OpenARDF/Arducon/Software/AtmelStudio7/Arducon/Arducon/EepromManager.cpp

/*
 *  MIT License
 *
 *  Copyright (c) 2021 DigitalConfections
 *
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
 *  THE SOFTWARE IS PROVIDED "AS IS", WITHOUT WARRANTY OF ANY KIND, EXPRESS OR
 *  IMPLIED, INCLUDING BUT NOT LIMITED TO THE WARRANTIES OF MERCHANTABILITY,
 *  FITNESS FOR A PARTICULAR PURPOSE AND NONINFRINGEMENT. IN NO EVENT SHALL THE
 *  AUTHORS OR COPYRIGHT HOLDERS BE LIABLE FOR ANY CLAIM, DAMAGES OR OTHER
 *  LIABILITY, WHETHER IN AN ACTION OF CONTRACT, TORT OR OTHERWISE, ARISING FROM,
 *  OUT OF OR IN CONNECTION WITH THE SOFTWARE OR THE USE OR OTHER DEALINGS IN THE
 *  SOFTWARE.
 */


#include "EepromManager.h"
#include "linkbus.h"
#include "i2c.h"

#if INCLUDE_RV3028_SUPPORT
#include "rv3028.h"
#endif

#if INCLUDE_DS3231_SUPPORT
#include "ds3231.h"
#endif

#ifdef ATMEL_STUDIO_7
#include <avr/pgmspace.h>
#include <avr/wdt.h>
#include <util/delay.h>
#include <stdio.h>
#include <string.h>
#include <math.h>
#endif  /* ATMEL_STUDIO_7 */

const char PRODUCT_NAME_LONG[] PROGMEM = PRODUCT_NAME_LONG_TXT;
const char HELP_TEXT[] PROGMEM = HELP_TEXT_TXT;
const char TEXT_SET_TIME[] PROGMEM = TEXT_SET_TIME_TXT;
const char TEXT_SET_START[] PROGMEM = TEXT_SET_START_TXT;
const char TEXT_SET_FINISH[] PROGMEM = TEXT_SET_FINISH_TXT;
const char TEXT_SET_ID[] PROGMEM = TEXT_SET_ID_TXT;
const char TEXT_ERR_FINISH_BEFORE_START[] PROGMEM = TEXT_ERR_FINISH_BEFORE_START_TXT;
const char TEXT_ERR_FINISH_IN_PAST[] PROGMEM = TEXT_ERR_FINISH_IN_PAST_TXT;
const char TEXT_ERR_START_IN_PAST[] PROGMEM = TEXT_ERR_START_IN_PAST_TXT;
const char TEXT_ERR_INVALID_TIME[] PROGMEM = TEXT_ERR_INVALID_TIME_TXT;
const char TEXT_ERR_TIME_IN_PAST[] PROGMEM = TEXT_ERR_TIME_IN_PAST_TXT;


static const uint8_t DATA_MODULATION_DEFAULTS[SIZE_OF_DATA_MODULATION] PROGMEM =
{
	31, 31, 29, 27, 24, 21, 17, 14,
	10, 8, 5, 3, 2, 1, 1, 0,
	0, 0, 1, 1, 2, 3, 5, 7,
	10, 13, 17, 20, 24, 27, 29, 31
};

/***********************************************************************
 * Global Variables & String Constants
 *
 * Identify each global with a "g_" prefix
 * Whenever possible limit globals' scope to this file using "static"
 * Use "volatile" for globals shared between ISRs and foreground loop
 ************************************************************************/

const struct EE_prom EEMEM EepromManager::ee_vars =
{
	/* .eeprom_initialization_flag = */ 0,
	/* .eeprom_layout_version = */ 0,
	/* .temperature_table = */ { 0 },
	/* .atmega_temp_calibration = */ 0,
	/* .thermal_shutdown_temperature_c = */ 0,
	/* .max_ever_temperature_tenths = */ 0,
	/* .rv3028_offset = */ 0,
	/* .event_start_epoch = */ 0,
	/* .event_finish_epoch = */ 0,
	/* .days_to_run = */ 0,
	/* .stationID_text = */ "\0",

	/* .dataModulation = */ { 0 },
	/* .unlockCode = */ EEPROM_DTMF_UNLOCK_CODE_DEFAULT,

	/* .id_codespeed = */ 0,
	/* .fox_setting = */ 0,
	/* .am_audio_frequency = */ 0,
	/* .utc_offset = */ 0,
	/* .ptt_periodic_reset = */ 0
};

extern char g_messages_text[][MAX_PATTERN_TEXT_LENGTH + 1];
extern volatile uint8_t g_id_codespeed;
extern volatile uint8_t g_pattern_codespeed;
extern volatile uint16_t g_time_needed_for_ID;
extern volatile int16_t g_atmega_temp_calibration;
extern volatile int8_t g_thermal_shutdown_temperature_c;
extern volatile int16_t g_max_ever_temperature_tenths;
extern volatile uint8_t g_temperature_check_countdown;
extern volatile int16_t g_rv3028_offset;

extern volatile Fox_t g_fox;
extern volatile AM_Tone_Freq_t g_AM_audio_frequency;
extern volatile time_t g_event_start_epoch;
extern volatile time_t g_event_finish_epoch;
extern volatile uint8_t g_days_to_run;
extern volatile int8_t g_utc_offset;
extern volatile uint8_t g_ptt_periodic_reset_enabled;

extern uint8_t g_dataModulation[];
extern uint8_t g_unlockCode[];

extern char g_tempStr[];

#define EEPROM_TEXT_TX_IDLE_WAIT_LIMIT 1000

static uint8_t eepromReadByteOrDefault(
	const uint8_t *address,
	uint8_t minimum,
	uint8_t maximum,
	uint8_t defaultValue)
{
	uint8_t value = eeprom_read_byte(address);

	if((value < minimum) || (value > maximum))
	{
		value = defaultValue;
		eeprom_write_byte((uint8_t*)address, value);
	}

	return value;
}

static uint8_t eepromReadBoolOrDefault(
	const uint8_t *address,
	uint8_t defaultValue)
{
	uint8_t value = eeprom_read_byte(address);

	if(value > 1)
	{
		value = defaultValue;
		eeprom_write_byte((uint8_t*)address, value);
	}

	return value;
}

/* default constructor */
EepromManager::EepromManager()
{
}   /*EepromManager */

/* default destructor */
EepromManager::~EepromManager()
{
}   /*~EepromManager */

void EepromManager::updateEEPROMVar(EE_var_t v, void* val)
{
	uint8_t* ee_byte_addr = NULL;
	uint16_t* ee_word_addr = NULL;
	uint32_t* ee_dword_addr = NULL;

	if(!val)
	{
		return;
	}

	switch(v)
	{
		case StationID_text:
		{
			char* char_addr = (char*)val;
			char c = *char_addr++;
			int i = 0;

			while(c && (i < MAX_PATTERN_TEXT_LENGTH))
			{
				eeprom_update_byte((uint8_t*)&(EepromManager::ee_vars.stationID_text[i++]), (uint8_t)c);
				c = *char_addr++;
			}

			eeprom_update_byte((uint8_t*)&(EepromManager::ee_vars.stationID_text[i]), 0);
		}
		break;

		case UnlockCode:
		{
			uint8_t* uint8_addr = (uint8_t*)val;
			uint8_t c = *uint8_addr++;
			int i = 0;

			while(c && (i < MAX_UNLOCK_CODE_LENGTH))
			{
				eeprom_update_byte((uint8_t*)&(EepromManager::ee_vars.unlockCode[i++]), c);
				c = *uint8_addr++;
			}

			eeprom_update_byte((uint8_t*)&(EepromManager::ee_vars.unlockCode[i]), 0);
		}
		break;

		case Id_codespeed:
		{
			ee_byte_addr = (uint8_t*)&(EepromManager::ee_vars.id_codespeed);
		}
		break;

		case Fox_setting:
		{
			ee_byte_addr = (uint8_t*)&(EepromManager::ee_vars.fox_setting);
		}
		break;

		case Am_audio_frequency:
		{
			ee_byte_addr = (uint8_t*)&(EepromManager::ee_vars.am_audio_frequency);
		}
		break;

		case Atmega_temp_calibration:
		{
			ee_word_addr = (uint16_t*)&(EepromManager::ee_vars.atmega_temp_calibration);
		}
		break;

		case Thermal_shutdown_temperature_c:
		{
			ee_byte_addr = (uint8_t*)&(EepromManager::ee_vars.thermal_shutdown_temperature_c);
		}
		break;

		case Max_ever_temperature_tenths:
		{
			ee_word_addr = (uint16_t*)&(EepromManager::ee_vars.max_ever_temperature_tenths);
		}
		break;

		case Rv3028_offset:
		{
			ee_word_addr = (uint16_t*)&(EepromManager::ee_vars.rv3028_offset);
		}
		break;

		case Event_start_epoch:
		{
			ee_dword_addr = (uint32_t*)&(EepromManager::ee_vars.event_start_epoch);
		}
		break;

		case Event_finish_epoch:
		{
			ee_dword_addr = (uint32_t*)&(EepromManager::ee_vars.event_finish_epoch);
		}
		break;

		case Days_to_run:
		{
			ee_byte_addr = (uint8_t*)&(EepromManager::ee_vars.days_to_run);
		}
		break;

		case Utc_offset:
		{
			ee_byte_addr = (uint8_t*)&(EepromManager::ee_vars.utc_offset);
		}
		break;

		case Ptt_periodic_reset:
		{
			ee_byte_addr = (uint8_t*)&(EepromManager::ee_vars.ptt_periodic_reset);
		}
		break;

		case Eeprom_initialization_flag:
		{
			ee_word_addr = (uint16_t*)&(EepromManager::ee_vars.eeprom_initialization_flag);
		}
		break;

		default:
		{

		}
		break;
	}

	if(ee_byte_addr)
	{
		eeprom_update_byte(ee_byte_addr, *(uint8_t*)val);
	}
	else if(ee_word_addr)
	{
		eeprom_update_word(ee_word_addr, *(uint16_t*)val);
	}
	else if(ee_dword_addr)
	{
		eeprom_update_dword(ee_dword_addr, *(uint32_t*)val);
	}
}

void EepromManager::sendEEPROMString(EE_var_t v)
{
	const char* fl_addr = NULL;

	if(!lb_enabled())
	{
		return;
	}

	switch(v)
	{
		case TextVersion:
		{
			fl_addr = PRODUCT_NAME_LONG;
		}
		break;

		case TextHelp:
		{
			fl_addr = HELP_TEXT;
		}
		break;

		case TextSetTime:
		{
			fl_addr = TEXT_SET_TIME;
		}
		break;

		case TextSetStart:
		{
			fl_addr = TEXT_SET_START;
		}
		break;

		case TextSetFinish:
		{
			fl_addr = TEXT_SET_FINISH;
		}
		break;

		case TextSetID:
		{
			fl_addr = TEXT_SET_ID;
		}
		break;

		case TextErrFinishB4Start:
		{
			fl_addr = TEXT_ERR_FINISH_BEFORE_START;

		}
		break;

		case TextErrFinishInPast:
		{
			fl_addr = TEXT_ERR_FINISH_IN_PAST;
		}
		break;

		case TextErrStartInPast:
		{
			fl_addr = TEXT_ERR_START_IN_PAST;
		}
		break;

		case TextErrInvalidTime:
		{
			fl_addr = TEXT_ERR_INVALID_TIME;
		}
		break;

		case TextErrTimeInPast:
		{
			fl_addr = TEXT_ERR_TIME_IN_PAST;
		}
		break;

		default:
		{

		}
		break;
	}

	if(fl_addr)
	{
		char c = pgm_read_byte(fl_addr++);
		uint16_t tries = EEPROM_TEXT_TX_IDLE_WAIT_LIMIT;

		while(c)
		{
			lb_echo_char(c);
			c = pgm_read_byte(fl_addr++);

			while(linkbusTxInProgress() && tries)
			{
				_delay_us(100);
				tries--;
			}

			if(!tries)
			{
				break;
			}

			tries = EEPROM_TEXT_TX_IDLE_WAIT_LIMIT;
		}
	}
}

BOOL EepromManager::readNonVols(void)
{
	BOOL failure = TRUE;
	uint16_t i;

	if(eepromLayoutIsCurrent())  /* EEPROM is initialized and matches this firmware layout */
	{
		g_id_codespeed = eepromReadByteOrDefault(
			&(EepromManager::ee_vars.id_codespeed),
			MIN_CODE_SPEED_WPM,
			MAX_CODE_SPEED_WPM,
			EEPROM_ID_CODE_SPEED_DEFAULT);
		g_fox = CLAMP(BEACON, (Fox_t)eeprom_read_byte(&(EepromManager::ee_vars.fox_setting)), SPRINT_F5);
		g_AM_audio_frequency = (AM_Tone_Freq_t)eepromReadByteOrDefault(
			&(EepromManager::ee_vars.am_audio_frequency),
			MIN_AM_TONE_FREQUENCY,
			MAX_AM_TONE_FREQUENCY,
			EEPROM_AM_AUDIO_FREQ_DEFAULT);
		g_atmega_temp_calibration = (int16_t)eeprom_read_word((uint16_t*)&(EepromManager::ee_vars.atmega_temp_calibration));
		g_thermal_shutdown_temperature_c = CLAMP(THERMAL_SHUTDOWN_MIN_C, (int8_t)eeprom_read_byte((uint8_t*)&(EepromManager::ee_vars.thermal_shutdown_temperature_c)), THERMAL_SHUTDOWN_MAX_C);
		g_max_ever_temperature_tenths = (int16_t)eeprom_read_word((uint16_t*)&(EepromManager::ee_vars.max_ever_temperature_tenths));
		g_rv3028_offset = (int16_t)eeprom_read_word((uint16_t*)&(EepromManager::ee_vars.rv3028_offset));
		g_event_start_epoch = eeprom_read_dword(&(EepromManager::ee_vars.event_start_epoch));
		g_event_finish_epoch = eeprom_read_dword(&(EepromManager::ee_vars.event_finish_epoch));
		g_days_to_run = eepromReadByteOrDefault(
			&(EepromManager::ee_vars.days_to_run),
			MIN_DAYS_TO_RUN,
			MAX_DAYS_TO_RUN,
			EEPROM_DAYS_TO_RUN_DEFAULT);
#if INCLUDE_RV3028_SUPPORT
		g_utc_offset = (int8_t)eeprom_read_byte(&(EepromManager::ee_vars.utc_offset));
		if((g_utc_offset < -24) || (g_utc_offset > 24))
		{
			g_utc_offset = EEPROM_UTC_OFFSET_DEFAULT;
			eeprom_write_byte((uint8_t*)&(EepromManager::ee_vars.utc_offset), (uint8_t)g_utc_offset);
		}
#else
		g_utc_offset = EEPROM_UTC_OFFSET_DEFAULT;
		if(eeprom_read_byte(&(EepromManager::ee_vars.utc_offset)) != (uint8_t)EEPROM_UTC_OFFSET_DEFAULT)
		{
			eeprom_write_byte((uint8_t*)&(EepromManager::ee_vars.utc_offset), (uint8_t)EEPROM_UTC_OFFSET_DEFAULT);
		}
#endif
		g_ptt_periodic_reset_enabled = eepromReadBoolOrDefault(
			&(EepromManager::ee_vars.ptt_periodic_reset),
			EEPROM_PTT_PERIODIC_RESET_DEFAULT);

		for(i = 0; i < MAX_PATTERN_TEXT_LENGTH; i++)
		{
			g_messages_text[STATION_ID][i] = (char)eeprom_read_byte((uint8_t*)(&(EepromManager::ee_vars.stationID_text[i])));
			if(!g_messages_text[STATION_ID][i])
			{
				break;
			}
		}
		g_messages_text[STATION_ID][MAX_PATTERN_TEXT_LENGTH] = '\0';

		for(i = 0; i < MAX_UNLOCK_CODE_LENGTH; i++)
		{
			g_unlockCode[i] = (char)eeprom_read_byte((uint8_t*)(&(EepromManager::ee_vars.unlockCode[i])));
			if(!g_unlockCode[i])
			{
				break;
			}
		}
		g_unlockCode[MAX_UNLOCK_CODE_LENGTH] = '\0';

		for(i = 0; i < SIZE_OF_DATA_MODULATION; i++)    /* Use 1-degree steps and take advantage of parabola symmetry for -35C to +85C coverage */
		{
			g_dataModulation[i] = (uint8_t)eeprom_read_byte((uint8_t*)&(EepromManager::ee_vars.dataModulation[i]));
		}

		/* Perform sanity checks */
		if(g_event_start_epoch && (g_event_finish_epoch <= g_event_start_epoch))
		{
			g_event_finish_epoch = g_event_start_epoch + SECONDS_24H;
		}

		failure = FALSE;
	}

	return( failure);
}

BOOL EepromManager::eepromLayoutIsCurrent(void)
{
	uint16_t initialization_flag = eeprom_read_word(&(EepromManager::ee_vars.eeprom_initialization_flag));
	uint16_t layout_version = eeprom_read_word(&(EepromManager::ee_vars.eeprom_layout_version));

	return((initialization_flag == EEPROM_INITIALIZED_FLAG) && (layout_version == EEPROM_LAYOUT_VERSION));
}


/*
 * Initialize EEPROM defaults and mirror mutable defaults into RAM.
 */
BOOL EepromManager::initializeEEPROMVars(void)
{
	uint16_t i;

	g_id_codespeed = EEPROM_ID_CODE_SPEED_DEFAULT;
	eeprom_write_byte((uint8_t*)&(EepromManager::ee_vars.id_codespeed), g_id_codespeed);

		g_fox = EEPROM_FOX_SETTING_DEFAULT;
		eeprom_write_byte((uint8_t*)&(EepromManager::ee_vars.fox_setting), g_fox);

		g_AM_audio_frequency = EEPROM_AM_AUDIO_FREQ_DEFAULT;
		eeprom_write_byte((uint8_t*)&(EepromManager::ee_vars.am_audio_frequency), (uint8_t)g_AM_audio_frequency);

		g_atmega_temp_calibration = EEPROM_TEMP_CALIBRATION_DEFAULT;
		eeprom_write_word((uint16_t*)&(EepromManager::ee_vars.atmega_temp_calibration), (uint16_t)g_atmega_temp_calibration);

		g_thermal_shutdown_temperature_c = EEPROM_THERMAL_SHUTDOWN_TEMP_C_DEFAULT;
		eeprom_write_byte((uint8_t*)&(EepromManager::ee_vars.thermal_shutdown_temperature_c), (uint8_t)g_thermal_shutdown_temperature_c);

		g_max_ever_temperature_tenths = EEPROM_MAX_EVER_TEMPERATURE_TENTHS_DEFAULT;
		eeprom_write_word((uint16_t*)&(EepromManager::ee_vars.max_ever_temperature_tenths), (uint16_t)g_max_ever_temperature_tenths);

		i2c_init(); /* Needs to happen before reading RTC */

#if INCLUDE_RV3028_SUPPORT
		g_rv3028_offset = rv3028_get_offset_RAM();
		eeprom_write_word((uint16_t*)&(EepromManager::ee_vars.rv3028_offset), (uint16_t)g_rv3028_offset);
#endif // INCLUDE_RV3028_SUPPORT

		g_event_start_epoch = EEPROM_START_EPOCH_DEFAULT;
		eeprom_write_dword((uint32_t*)&(EepromManager::ee_vars.event_start_epoch), g_event_start_epoch);

		g_event_finish_epoch = EEPROM_FINISH_EPOCH_DEFAULT;
		eeprom_write_dword((uint32_t*)&(EepromManager::ee_vars.event_finish_epoch), g_event_finish_epoch);

		g_days_to_run = EEPROM_DAYS_TO_RUN_DEFAULT;
		eeprom_write_byte((uint8_t*)&(EepromManager::ee_vars.days_to_run), g_days_to_run);

		g_utc_offset = EEPROM_UTC_OFFSET_DEFAULT;
		eeprom_write_byte((uint8_t*)&(EepromManager::ee_vars.utc_offset), (uint8_t)g_utc_offset);

		g_ptt_periodic_reset_enabled = EEPROM_PTT_PERIODIC_RESET_DEFAULT;
		eeprom_write_byte((uint8_t*)&(EepromManager::ee_vars.ptt_periodic_reset), g_ptt_periodic_reset_enabled);

		g_messages_text[STATION_ID][0] = '\0';
		eeprom_write_byte((uint8_t*)&(EepromManager::ee_vars.stationID_text[0]), 0);

		uint8_t *v = (uint8_t*)EEPROM_DTMF_UNLOCK_CODE_DEFAULT;
		for(i = 0; i < strlen(EEPROM_DTMF_UNLOCK_CODE_DEFAULT); i++)
		{
			g_unlockCode[i] = *v;
			eeprom_write_byte((uint8_t*)&(EepromManager::ee_vars.unlockCode[i]), *v++);
		}

		eeprom_write_byte((uint8_t*)&(EepromManager::ee_vars.unlockCode[i]), 0);
		g_unlockCode[i] = '\0';

		/* Each correction pulse = 1 tick corresponds to 1 / (16384 x 64) = 0.9537 ppm.
		 * ppm frequency change = -0.035 * (T-T0)^2 (+/-10%)
		 * Table[0] = 25C, Table[1] = 24C or 26C, Table[2] = 23C or 27C, etc. */
		for(i = 0; i < SIZE_OF_TEMPERATURE_TABLE; i++)  /* Use 1-degree steps and take advantage of parabola symmetry for -35C to +85C coverage */
		{
			uint16_t val = (uint16_t)(((i * i) * 37L) / 1000L);
			eeprom_write_word((uint16_t*)&(EepromManager::ee_vars.temperature_table[i]), val);
		}

	for(i = 0; i < SIZE_OF_DATA_MODULATION; i++)
	{
		eeprom_write_byte((uint8_t*)&(EepromManager::ee_vars.dataModulation[i]), pgm_read_byte(&DATA_MODULATION_DEFAULTS[i]));
	}

		/* Done */

		eeprom_write_word((uint16_t*)&(EepromManager::ee_vars.eeprom_layout_version), EEPROM_LAYOUT_VERSION);
		eeprom_write_word((uint16_t*)&(EepromManager::ee_vars.eeprom_initialization_flag), EEPROM_INITIALIZED_FLAG);

	return(FALSE);
}


void EepromManager::resetEEPROMValues(void)
{
	uint8_t i;

	uint8_t *v = (uint8_t*)EEPROM_DTMF_UNLOCK_CODE_DEFAULT;
	for(i = 0; i < strlen(EEPROM_DTMF_UNLOCK_CODE_DEFAULT); i++)
	{
		g_unlockCode[i] = *v;
		eeprom_write_byte((uint8_t*)&(EepromManager::ee_vars.unlockCode[i]), *v++);
	}

	eeprom_write_byte((uint8_t*)&(EepromManager::ee_vars.unlockCode[i]), 0);
	g_unlockCode[i] = '\0';

	g_messages_text[STATION_ID][0] = '\0';
	eeprom_write_byte((uint8_t*)&(EepromManager::ee_vars.stationID_text[0]), 0);

	g_AM_audio_frequency = EEPROM_AM_AUDIO_FREQ_DEFAULT;
	eeprom_write_byte((uint8_t*)&(EepromManager::ee_vars.am_audio_frequency), (uint8_t)g_AM_audio_frequency);

	g_event_start_epoch = EEPROM_START_EPOCH_DEFAULT;
	eeprom_write_dword((uint32_t*)&(EepromManager::ee_vars.event_start_epoch), g_event_start_epoch);

	g_event_finish_epoch = EEPROM_FINISH_EPOCH_DEFAULT;
	eeprom_write_dword((uint32_t*)&(EepromManager::ee_vars.event_finish_epoch), g_event_finish_epoch);

	g_days_to_run = EEPROM_DAYS_TO_RUN_DEFAULT;
	eeprom_write_byte((uint8_t*)&(EepromManager::ee_vars.days_to_run), g_days_to_run);
}

/***********************************************************************
 * send_Help(void)
 ************************************************************************/
void EepromManager::send_Help(void)
{

	lb_send_NewLine();
	sendEEPROMString(TextVersion);
	sendEEPROMString(TextHelp);
	lb_send_NewLine();
	lb_send_NewLine();
}

uint16_t EepromManager::readTemperatureTable(int i)
{
	return( (uint16_t)eeprom_read_word(&(EepromManager::ee_vars.temperature_table[i])));
}
