OpenARDF/Arducon/Software/AtmelStudio7/Arducon/Arducon/rv3028.cpp

/**********************************************************************************************
 * Copyright (c) 2021 Digital Confections LLC
 *
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
 **********************************************************************************************
 * rv3028.c
 *
 */

#include "defs.h"
#ifdef ATMEL_STUDIO_7
#include <string.h>
#endif  /* ATMEL_STUDIO_7 */

#if INCLUDE_RV3028_SUPPORT

   #include "rv3028.h"
   #include <util/twi.h>
   #include <stdio.h>
   #include "i2c.h"
   #include "linkbus.h"

   #define RTC_SECONDS                     0x00
   #define RTC_MINUTES                     0x01
   #define RTC_HOURS                       0x02
   #define RTC_WEEKDAY                     0x03
   #define RTC_DATE                        0x04
   #define RTC_MONTH                       0x05
   #define RTC_YEAR                        0x06
   #define RTC_ALARM_MINUTES               0x07
   #define RTC_ALARM_HOURS                 0x08
   #define RTC_ALARM_DAY_DATE              0x09
   #define RTC_TIMER_VAL_0                 0x0A
   #define RTC_TIMER_VAL_1                 0x0B
   #define RTC_TIMER_STATUS_0              0x0C
   #define RTC_TIMER_STATUS_1              0x0D
   #define RTC_STATUS                      0x0E
   #define RTC_CONTROL_1                   0x0F
   #define RTC_CONTROL_2                   0x10
   #define RTC_GP_BITS                     0x11
   #define RTC_CLOCK_INT_MASK              0x12
   #define RTC_EVENT_CONTROL               0x13
   #define RTC_COUNT_TS                    0x14
   #define RTC_SECONDS_TS                  0x15
   #define RTC_MINUTES_TS                  0x16
   #define RTC_HOURS_TS                    0x17
   #define RTC_DATE_TS                     0x18
   #define RTC_MONTH_TS                    0x19
   #define RTC_YEAR_TS                     0x1A
   #define RTC_UNIX_TIME_0                 0x1B
   #define RTC_UNIX_TIME_1                 0x1C
   #define RTC_UNIX_TIME_2                 0x1D
   #define RTC_UNIX_TIME_3                 0x1E
   #define RTC_USER_RAM_1                  0x1F
   #define RTC_USER_RAM_2                  0x20
   #define RTC_PASSWORD_0                  0x21
   #define RTC_PASSWORD_1                  0x22
   #define RTC_PASSWORD_2                  0x23
   #define RTC_PASSWORD_3                  0x24
   #define RTC_EE_COMMAND                  0x27
   #define RTC_ID                          0x28
   #define RTC_EEPROM_CLKOUT               0x35
   #define RTC_EEPROM_OFFSET               0x36

   #define EEbusy 7


	static BOOL g_1HzSqWave_on = FALSE;

	BOOL waitForEEPROMReady(void);
	void refreshRAMfromEEPROM(void);

	uint8_t bcd2dec(uint8_t val)
	{
		uint8_t result = 10 * (val >> 4) + (val & 0x0F);

		return( result);
	}

	uint8_t char2bcd(char c[])
	{
		uint8_t result = (c[1] - '0') + ((c[0] - '0') << 4);

		return( result);
	}

	BOOL waitForEEPROMReady(void)
	{
		uint8_t status = 1;
		BOOL failure = FALSE;

		while(status && !failure)
		{
			failure |= i2c_device_read(RV3028_I2C_SLAVE_ADDR, RTC_STATUS, &status, 1);
			if(!failure)
			{
				status &= (1 << EEbusy);
			}
		}

		return(status);
	}

	/* Note: this is not thread safe */
		time_t RTC_get_epoch(bool *result, char *datetime)
	{
		uint8_t data[7] = { 0, 0, 0, 0, 0, 0, 0 };
		BOOL res = 0;
		time_t epoch = 0;

		if(datetime)                            /* String format "YYMMDDhhmmss" */
		{
			data[0] = char2bcd(&datetime[10]);  /* seconds in BCD */
			data[1] = char2bcd(&datetime[8]);   /* minutes in BCD */
			data[2] = char2bcd(&datetime[6]);   /* hours in BCD */
			/* data[3] =  not used */
			data[4] = char2bcd(&datetime[4]);   /* day of month in BCD */
			data[5] = char2bcd(&datetime[2]);   /* month in BCD */
			data[6] = char2bcd(&datetime[0]);   /* 2-digit year in BCD */

			struct tm ltm = { 0, 0, 0, 0, 0, 0, 0, 0, 0 };
			int16_t year = 100;                 /* start at 100 years past 1900 */
			uint8_t month;
			uint8_t date;
			uint8_t hours;
			uint8_t minutes;
			uint8_t seconds;

			year += (int16_t)bcd2dec(data[6]);
			ltm.tm_year = year;                         /* year since 1900 */

			year += 1900;                               /* adjust year to calendar year */

			month = bcd2dec(data[5]);
			ltm.tm_mon = month - 1;                     /* mon 0 to 11 */

			date = bcd2dec(data[4]);
			ltm.tm_mday = date;                         /* month day 1 to 31 */

			ltm.tm_yday = 0;
			for(uint8_t mon = 1; mon < month; mon++)    /* months from 1 to 11 (excludes partial month) */
			{
				ltm.tm_yday += month_length(year, mon);;
			}

			ltm.tm_yday += (ltm.tm_mday - 1);

			seconds = bcd2dec(data[0]);
			minutes = bcd2dec(data[1]);
			hours = bcd2dec(data[2]);

			ltm.tm_hour = hours;
			ltm.tm_min = minutes;
			ltm.tm_sec = seconds;

			epoch = ltm.tm_sec + ltm.tm_min * 60 + ltm.tm_hour * 3600L + ltm.tm_yday * 86400L +
					(ltm.tm_year - 70) * 31536000L + ((ltm.tm_year - 69) / 4) * 86400L -
					((ltm.tm_year - 1) / 100) * 86400L + ((ltm.tm_year + 299) / 400) * 86400L;
		}
		else
		{
/*			res = i2c_device_read(RV3028_I2C_SLAVE_ADDR, RTC_SECONDS, data, 7); */
			epoch = RTC_get_epoch();
			res = epoch == 0;
		}

		if(result)
		{
			*result = res ? 1 : 0;
		}

		return(epoch);
	}

#ifdef DATE_STRING_SUPPORT_ENABLED
		void rv3028_read_date_time(int32_t* val, char* buffer, TimeFormat format)
		{
			uint8_t data[7] = { 0, 0, 0, 0, 0, 0, 0 };
			uint8_t month;
			uint8_t date;
			uint16_t year = 2000;
			uint8_t seconds;
			uint8_t minutes;
			uint8_t hours;

			if(!i2c_device_read(RV3028_I2C_SLAVE_ADDR, RTC_SECONDS, data, 7))
			{
				seconds = bcd2dec(data[0]);
				minutes = bcd2dec(data[1]);
				hours = bcd2dec(data[2]);

				if(buffer)
				{
					switch(format)
					{
						case Minutes_Seconds:
						{
							sprintf(buffer, "%1d:%1d", minutes, seconds);
						}
						break;

						case Hours_Minutes_Seconds:
						{
							sprintf(buffer, "%1d:%1d:%1d", hours, minutes, seconds);

						}
						break;

						default:    /* Day_Month_Year_Hours_Minutes_Seconds: */
						{
							date = bcd2dec(data[4]);
							month = bcd2dec(data[5]);
							year += bcd2dec(data[6]);

							sprintf(buffer, "%4d-%02d-%02dT%1d:%1d:%1d", year, month, date, hours, minutes, seconds);
						}
						break;
					}
				}

				if(val)
				{
					*val = seconds + 60 * (int32_t)minutes +  3600 * (int32_t)hours;
				}
			}
		}
#endif  /* DATE_STRING_SUPPORT_ENABLED */

	BOOL RTC_set_epoch(time_t epoch)
	{
		uint8_t data[5] = { 0, 0, 0, 0 };

		data[3] = (uint8_t)((epoch & 0xff000000) >> 24);
		data[2] = (uint8_t)((epoch & 0x00ff0000) >> 16);
		data[1] = (uint8_t)((epoch & 0x0000ff00) >> 8);
		data[0] = (uint8_t)((epoch & 0x000000ff));
		return(i2c_device_write(RV3028_I2C_SLAVE_ADDR, RTC_UNIX_TIME_0, data, 4));
	}

	time_t RTC_get_epoch(void)
	{
		time_t epoch = 0;
		uint8_t data[4] = { 0, 0, 0, 0 };

		if(!i2c_device_read(RV3028_I2C_SLAVE_ADDR, RTC_UNIX_TIME_0, data, 4))
		{
			epoch |= data[0];
			epoch |= ((time_t)data[1]) << 8;
			epoch |= ((time_t)data[2]) << 16;
			epoch |= ((time_t)data[3]) << 24;
		}

		return( epoch);
	}


// 	BOOL rv3028_set_date_time(char * dateString)                                                                                         /* String format "YYMMDDhhmmss" */
// 	{
// 		BOOL fail = TRUE;
// 		uint8_t data[7] = { 0, 0, 0, 1, 0, 0, 0 };
// 		int length = strlen((const char*)dateString);
//
// 		if(length >= 12)
// 		{
// 			data[0] = dateString[11] - '0';             /* seconds */
// 			data[0] += ((dateString[10] - '0') << 4);   /* 10s of seconds */
// 			data[1] = dateString[9] - '0';              /* minutes */
// 			data[1] += ((dateString[8] - '0') << 4);    /* 10s of minutes */
// 			data[2] = dateString[7] - '0';              /* hours */
// 			data[2] += ((dateString[6] - '0') << 4);    /* 10s of hours */
//
// 			/*data[3] = Skip day of week */
//
// 			data[4] = dateString[5] - '0';              /* day of month digit 1 */
// 			data[4] += ((dateString[4] - '0') << 4);    /* day of month */
// 			data[5] = dateString[3] - '0';              /* month digit 1 */
// 			data[5] += ((dateString[2] - '0') << 4);    /* month */
// 			data[6] = dateString[1] - '0';              /* year digit 1 */
// 			data[6] += ((dateString[0] - '0') << 4);    /* year - two digits */
//
// 			fail = i2c_device_write(RV3028_I2C_SLAVE_ADDR, RTC_SECONDS, data, 7);
// 		}
//
// 		return( fail);
// 	}


	void refreshRAMfromEEPROM(void)
	{
		uint8_t status = FALSE;
		uint8_t temp = 0;

		status = i2c_device_write(RV3028_I2C_SLAVE_ADDR, RTC_EE_COMMAND, &temp, 1);
		waitForEEPROMReady();
		temp = 0x12;    /* Refresh RAM from EEPROM */
		status |= i2c_device_write(RV3028_I2C_SLAVE_ADDR, RTC_EE_COMMAND, &temp, 1);
		waitForEEPROMReady();
	}

	int16_t rv3028_get_offset_RAM()
	{
		uint8_t data[2];
		int16_t result;

		refreshRAMfromEEPROM(); /* Ensure we never return an altered RAM value */
		i2c_device_read(RV3028_I2C_SLAVE_ADDR, RTC_EEPROM_OFFSET, (uint8_t*)data, 2);
		result = data[0] << 1;
		if(data[1] & 0x80)
		{
			result++;
		}
		return(result);
	}

	void rv3028_set_offset_RAM(uint16_t val)
	{
		uint8_t data[2] = { 0, 0x10 };

		data[0] = val >> 1;
		if(val & 0x01)
		{
			data[1] = 0x90;
		}

		i2c_device_write(RV3028_I2C_SLAVE_ADDR, RTC_EEPROM_OFFSET, (uint8_t*)data, 2);
	}

		BOOL RTC_1s_sqw(BOOL onOff)
		{
			uint8_t status = FALSE;
			uint8_t temp = onOff; /* remove compile warning */

				if(onOff)
				{
					temp = 0xC5;    /* turn on 1-Hz signal */
					g_1HzSqWave_on = TRUE;
				}
				else
				{
					temp = 0x45;    /* turn off 1-Hz signal */
					g_1HzSqWave_on = FALSE;
				}

				i2c_device_write(RV3028_I2C_SLAVE_ADDR, RTC_EEPROM_CLKOUT, &temp, 1);

			if(!status)
			{
				temp = i2c_device_read(RV3028_I2C_SLAVE_ADDR, RTC_STATUS, &status, 1);
				status &= 0x6F; /* Mask off relevant flags: 01101111 */
			}
			else
			{
				status = 1 << RTC_STATUS_I2C_ERROR;
			}

			temp = 0x00;    /* Clear status flags */
			i2c_device_write(RV3028_I2C_SLAVE_ADDR, RTC_STATUS, &temp, 1);

			return(status);
		}
	BOOL rv3028_1Hz_enabled(void)
	{
		return(g_1HzSqWave_on);
	}
#endif  /* #ifdef INCLUDE_RV3028_SUPPORT */
