OpenARDF/Arducon/Software/AtmelStudio7/Arducon/Arducon/ardooweeno.cpp

/*
 *  MIT License
 *
 *  Copyright (c) 2020 DigitalConfections
 *
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
 *  THE SOFTWARE IS PROVIDED "AS IS", WITHOUT WARRANTY OF ANY KIND, EXPRESS OR
 *  IMPLIED, INCLUDING BUT NOT LIMITED TO THE WARRANTIES OF MERCHANTABILITY,
 *  FITNESS FOR A PARTICULAR PURPOSE AND NONINFRINGEMENT. IN NO EVENT SHALL THE
 *  AUTHORS OR COPYRIGHT HOLDERS BE LIABLE FOR ANY CLAIM, DAMAGES OR OTHER
 *  LIABILITY, WHETHER IN AN ACTION OF CONTRACT, TORT OR OTHERWISE, ARISING FROM,
 *  OUT OF OR IN CONNECTION WITH THE SOFTWARE OR THE USE OR OTHER DEALINGS IN THE
 *  SOFTWARE.
 */

#include "ardooweeno.h"
#include <util/delay.h>

void pinMode(uint8_t pin, uint8_t mode)
{
	switch(pin)
	{
		case PIN_RXD:
		{
			if(mode == OUTPUT)
			{
				DDRD  |= (1 << PORTD0);
			}
			else
			{
				DDRD  &= ~(1 << PORTD0);

				if(mode == INPUT_PULLUP)
				{
					PORTD  |= (1 << PORTD0);
				}
				else
				{
					PORTD &= ~(1 << PORTD0);
				}
			}
		}
		break;
		
		case PIN_TXD:
		{
			if(mode == OUTPUT)
			{
				DDRD  |= (1 << PORTD1);
			}
			else
			{
				DDRD  &= ~(1 << PORTD1);

				if(mode == INPUT_PULLUP)
				{
					PORTD  |= (1 << PORTD1);
				}
				else
				{
					PORTD &= ~(1 << PORTD1);
				}
			}
		}
		break;
		
		case D2:
		{
			if(mode == OUTPUT)
			{
				DDRD  |= (1 << PORTD2);
			}
			else
			{
				DDRD  &= ~(1 << PORTD2);

				if(mode == INPUT_PULLUP)
				{
					PORTD  |= (1 << PORTD2);
				}
				else
				{
					PORTD &= ~(1 << PORTD2);
				}
			}
		}
		break;

		case D3:
		{
			if(mode == OUTPUT)
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

		case A2:
		{
			if(value)
			{
				PORTC  |= (1 << PORTC2);
			}
			else
			{
				PORTC  &= ~(1 << PORTC2);
			}
		}
		break;

		case A3:
		{
			if(value)
			{
				PORTC  |= (1 << PORTC3);
			}
			else
			{
				PORTC  &= ~(1 << PORTC3);
			}
		}
		break;

		default:
		{
		}
		break;
	}
}
