OpenARDF/Arducon/Software/AtmelStudio7/Arducon/Arducon/linkbus.cpp

/*
 *  MIT License
 *
 *  Copyright (c) 2021 DigitalConfections
 *
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
 *  THE SOFTWARE IS PROVIDED "AS IS", WITHOUT WARRANTY OF ANY KIND, EXPRESS OR
 *  IMPLIED, INCLUDING BUT NOT LIMITED TO THE WARRANTIES OF MERCHANTABILITY,
 *  FITNESS FOR A PARTICULAR PURPOSE AND NONINFRINGEMENT. IN NO EVENT SHALL THE
 *  AUTHORS OR COPYRIGHT HOLDERS BE LIABLE FOR ANY CLAIM, DAMAGES OR OTHER
 *  LIABILITY, WHETHER IN AN ACTION OF CONTRACT, TORT OR OTHERWISE, ARISING FROM,
 *  OUT OF OR IN CONNECTION WITH THE SOFTWARE OR THE USE OR OTHER DEALINGS IN THE
 *  SOFTWARE.
 */
/* linkbus.c
 *
 */

#include "defs.h"
#include "linkbus.h"


#ifdef ATMEL_STUDIO_7
#include <avr/eeprom.h>
#include <avr/wdt.h>
#include <util/delay.h>
#endif  /* ATMEL_STUDIO_7 */

#ifdef ATMEL_STUDIO_7
#include <string.h>
#include <stdio.h>
#endif  /* ATMEL_STUDIO_7 */

/* Global Variables */
static volatile BOOL g_bus_disabled = TRUE;
static const char crlf[] = "\n";
static const char textPrompt[] = "> ";

static char g_tempMsgBuff[LINKBUS_MAX_MSG_LENGTH];

/* Local function prototypes */
BOOL linkbus_start_tx(void);
BOOL linkbus_send_text(char* text);
BOOL linkbus_wait_for_tx_idle(void);

#define LINKBUS_TX_PAYLOAD_LENGTH (LINKBUS_MAX_TX_MSG_LENGTH - 1)
#define LINKBUS_TX_IDLE_WAIT_LIMIT 1000
#define LINKBUS_TX_IDLE_WAIT_US 100

/* Module global variables */
static volatile BOOL linkbus_tx_active = FALSE; /* volatile is required to ensure optimizer handles this properly */
static LinkbusTxBuffer tx_buffer[LINKBUS_NUMBER_OF_TX_MSG_BUFFERS];
static LinkbusRxBuffer rx_buffer[LINKBUS_NUMBER_OF_RX_MSG_BUFFERS];

LinkbusTxBuffer* nextFullTxBuffer(void)
{
	BOOL found = TRUE;
	static uint8_t bufferIndex = 0;
	uint8_t count = 0;

	while(tx_buffer[bufferIndex][0] == '\0')
	{
		if(++count >= LINKBUS_NUMBER_OF_TX_MSG_BUFFERS)
		{
			found = FALSE;
			break;
		}

		bufferIndex++;
		if(bufferIndex >= LINKBUS_NUMBER_OF_TX_MSG_BUFFERS)
		{
			bufferIndex = 0;
		}
	}

	if(found)
	{
		return( &tx_buffer[bufferIndex]);
	}

	return(null);
}

LinkbusTxBuffer* nextEmptyTxBuffer(void)
{
	BOOL found = TRUE;
	static uint8_t bufferIndex = 0;
	uint8_t count = 0;

	while(tx_buffer[bufferIndex][0] != '\0')
	{
		if(++count >= LINKBUS_NUMBER_OF_TX_MSG_BUFFERS)
		{
			found = FALSE;
			break;
		}

		bufferIndex++;
		if(bufferIndex >= LINKBUS_NUMBER_OF_TX_MSG_BUFFERS)
		{
			bufferIndex = 0;
		}
	}

	if(found)
	{
		return( &tx_buffer[bufferIndex]);
	}

	return(null);
}

LinkbusRxBuffer* nextEmptyRxBuffer(void)
{
	BOOL found = TRUE;
	static uint8_t bufferIndex = 0;
	uint8_t count = 0;

	while(rx_buffer[bufferIndex].id != MESSAGE_EMPTY)
	{
		if(++count >= LINKBUS_NUMBER_OF_RX_MSG_BUFFERS)
		{
			found = FALSE;
			break;
		}

		bufferIndex++;
		if(bufferIndex >= LINKBUS_NUMBER_OF_RX_MSG_BUFFERS)
		{
			bufferIndex = 0;
		}
	}

	if(found)
	{
		return( &rx_buffer[bufferIndex]);
	}

	return(null);
}

LinkbusRxBuffer* nextFullRxBuffer(void)
{
	BOOL found = TRUE;
	static uint8_t bufferIndex = 0;
	uint8_t count = 0;

	while(rx_buffer[bufferIndex].id == MESSAGE_EMPTY)
	{
		if(++count >= LINKBUS_NUMBER_OF_RX_MSG_BUFFERS)
		{
			found = FALSE;
			break;
		}

		bufferIndex++;
		if(bufferIndex >= LINKBUS_NUMBER_OF_RX_MSG_BUFFERS)
		{
			bufferIndex = 0;
		}
	}

	if(found)
	{
		return( &rx_buffer[bufferIndex]);
	}

	return(null);
}


/***********************************************************************
 * linkbusTxInProgress(void)
 ************************************************************************/
BOOL linkbusTxInProgress(void)
{
	return(linkbus_tx_active);
}

BOOL linkbus_start_tx(void)
{
	BOOL success = !linkbus_tx_active;

	if(success) /* message will be lost if transmit is busy */
	{
		linkbus_tx_active = TRUE;
		UCSR0B |= (1 << UDRIE0);
	}

	return(success);
}

void linkbus_end_tx(void)
{
	if(linkbus_tx_active)
	{
		UCSR0B &= ~(1 << UDRIE0);
		linkbus_tx_active = FALSE;
	}
}

// void linkbus_reset_rx(void)
// {
// 	if(UCSR0B & (1 << RXEN0))   /* perform only if rx is currently enabled */
// 	{
// 		UCSR0B &= ~(1 << RXEN0);
// 		memset(rx_buffer, 0, sizeof(rx_buffer));
// 		UCSR0B |= (1 << RXEN0);
// 	}
// }

void linkbus_init(uint32_t baud)
{
	memset(rx_buffer, 0, sizeof(rx_buffer));

	for(int bufferIndex = 0; bufferIndex < LINKBUS_NUMBER_OF_TX_MSG_BUFFERS; bufferIndex++)
	{
		tx_buffer[bufferIndex][0] = '\0';
	}

	/*Set baud rate */
	uint16_t myubrr = MYUBRR(baud);
	UBRR0H = (uint8_t)(myubrr >> 8);
	UBRR0L = (uint8_t)myubrr;
	/* Enable receiver and transmitter and related interrupts */
	UCSR0B = (1 << RXEN0) | (1 << TXEN0) | (1 << RXCIE0);
/*  UCSR0B = (1<<RXEN0) | (1<<TXEN0);
 * Set frame format: 8data, 2stop bit */
	UCSR0C = (1 << USBS0) | (3 << UCSZ00);
	g_bus_disabled = FALSE;
}

void linkbus_disable(void)
{
	uint8_t bufferIndex;

	g_bus_disabled = TRUE;
	UCSR0B = 0;
	linkbus_end_tx();
	memset(rx_buffer, 0, sizeof(rx_buffer));

	for(bufferIndex = 0; bufferIndex < LINKBUS_NUMBER_OF_TX_MSG_BUFFERS; bufferIndex++)
	{
		tx_buffer[bufferIndex][0] = '\0';
	}
}

// void linkbus_enable(void)
// {
// 	uint8_t bufferIndex;
//
// 	g_bus_disabled = FALSE;
// 	UCSR0B = (1 << RXEN0) | (1 << TXEN0) | (1 << RXCIE0);
//
// 	memset(rx_buffer, 0, sizeof(rx_buffer));
//
// 	for(bufferIndex = 0; bufferIndex < LINKBUS_NUMBER_OF_TX_MSG_BUFFERS; bufferIndex++)
// 	{
// 		tx_buffer[bufferIndex][0] = '\0';
// 	}
// }


BOOL linkbus_send_text(char* text)
{
	BOOL err = TRUE;
	uint16_t tries = LINKBUS_TX_IDLE_WAIT_LIMIT;

	if(g_bus_disabled)
	{
		return( err);
	}

	if(text)
	{
		LinkbusTxBuffer* buff = nextEmptyTxBuffer();

		if(!buff && !(SREG & (1 << SREG_I)))
		{
			return(err);
		}

		while(!buff && tries)
		{
			if(linkbusTxInProgress())
			{
				_delay_us(LINKBUS_TX_IDLE_WAIT_US); /* Wait for ISR-driven transmit progress without feeding the watchdog. */
				tries--;
			}
			else
			{
				tries = 0;
			}

			buff = nextEmptyTxBuffer();
		}

		if(buff)
		{
			strncpy(*buff, text, LINKBUS_TX_PAYLOAD_LENGTH);
			(*buff)[LINKBUS_TX_PAYLOAD_LENGTH] = '\0';

			linkbus_start_tx();
			err = FALSE;
		}
	}

	return(err);
}

BOOL linkbus_wait_for_tx_idle(void)
{
	uint16_t tries = LINKBUS_TX_IDLE_WAIT_LIMIT;

	if(!(SREG & (1 << SREG_I)))
	{
		return(linkbusTxInProgress());
	}

	while(linkbusTxInProgress() && tries)
	{
		_delay_us(LINKBUS_TX_IDLE_WAIT_US);
		tries--;
	}

	return(linkbusTxInProgress());
}


/***********************************************************************************
 *  Support for creating and sending various Terminal Mode Linkbus messages is provided below.
 ************************************************************************************/

void lb_send_NewPrompt(void)
{
	if(g_bus_disabled)
	{
		return;
	}

	linkbus_send_text((char*)textPrompt);
}

void lb_send_NewLine(void)
{
	if(g_bus_disabled)
	{
		return;
	}
	linkbus_send_text((char*)crlf);
}

void lb_echo_char(uint8_t c)
{
	if(g_bus_disabled)
	{
		return;
	}
	g_tempMsgBuff[0] = c;
	g_tempMsgBuff[1] = '\0';
	linkbus_send_text(g_tempMsgBuff);
}

BOOL lb_send_string(char* str, BOOL wait)
{
	BOOL err = FALSE;
	char* p = str;

	if(g_bus_disabled)
	{
		return( TRUE);
	}

	if(str == NULL)
	{
		return( TRUE);
	}

	if(!*str)
	{
		return(TRUE);
	}

	while(*p && !err)
	{
		size_t chunkLen = strlen(p);
		if(chunkLen > LINKBUS_TX_PAYLOAD_LENGTH)
		{
			chunkLen = LINKBUS_TX_PAYLOAD_LENGTH;
		}

		strncpy(g_tempMsgBuff, p, chunkLen);
		g_tempMsgBuff[chunkLen] = '\0';

		if(wait)
		{
			err = linkbus_send_text(g_tempMsgBuff);
			if(err)
			{
				break;
			}

			err = linkbus_wait_for_tx_idle();
			if(err)
			{
				break;
			}
		}
		else
		{
			err = linkbus_send_text(g_tempMsgBuff);
		}

		p += chunkLen;
	}

	return( err);
}

void lb_send_value(uint16_t value, char* label)
{
	BOOL err;

	if(g_bus_disabled)
	{
		return;
	}

	sprintf(g_tempMsgBuff, "> %s=%d\n", label, value);
	err = linkbus_send_text(g_tempMsgBuff);
	if(err)
	{
		return;
	}

	linkbus_wait_for_tx_idle();
}


BOOL lb_enabled(void)
{
	return( !g_bus_disabled);
}
