OpenARDF/Arducon/Software/AtmelStudio7/Arducon/Arducon/linkbus.h

/*
 *  MIT License
 *
 *  Copyright (c) 2021 DigitalConfections
 *
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
 *  THE SOFTWARE IS PROVIDED "AS IS", WITHOUT WARRANTY OF ANY KIND, EXPRESS OR
 *  IMPLIED, INCLUDING BUT NOT LIMITED TO THE WARRANTIES OF MERCHANTABILITY,
 *  FITNESS FOR A PARTICULAR PURPOSE AND NONINFRINGEMENT. IN NO EVENT SHALL THE
 *  AUTHORS OR COPYRIGHT HOLDERS BE LIABLE FOR ANY CLAIM, DAMAGES OR OTHER
 *  LIABILITY, WHETHER IN AN ACTION OF CONTRACT, TORT OR OTHERWISE, ARISING FROM,
 *  OUT OF OR IN CONNECTION WITH THE SOFTWARE OR THE USE OR OTHER DEALINGS IN THE
 *  SOFTWARE.
 */
/*
 * linkbus.h - a simple serial inter-processor communication protocol.
 */

#ifndef LINKBUS_H_
#define LINKBUS_H_

#include "defs.h"

#ifdef __cplusplus
	extern "C" {
#endif

#define LINKBUS_MAX_MSG_LENGTH 50
#define LINKBUS_MIN_MSG_LENGTH 2    /* shortest message: GO */
#define LINKBUS_MAX_MSG_FIELD_LENGTH 20
#define LINKBUS_MAX_MSG_NUMBER_OF_FIELDS 3
#define LINKBUS_NUMBER_OF_RX_MSG_BUFFERS 2
#define LINKBUS_MAX_TX_MSG_LENGTH 41
#define LINKBUS_NUMBER_OF_TX_MSG_BUFFERS 3

#define LINKBUS_MAX_COMMANDLINE_LENGTH ((1 + LINKBUS_MAX_MSG_FIELD_LENGTH) * LINKBUS_MAX_MSG_NUMBER_OF_FIELDS)

#define LINKBUS_POWERUP_DELAY_SECONDS 6

#define LINKBUS_MIN_TX_INTERVAL_MS 100

#define BAUD 57600
#define UPDATE_BAUD 115200
#define MYUBRR(b) ((F_CPU + b * 8L) / (b * 16L) - 1)

typedef enum
{
	EMPTY_BUFF,
	FULL_BUFF
} BufferState;

/*  Linkbus Messages
 *       Message formats:
 *               CMD [a1 [a2]]
 *
 *               where
 *                       CMD = command
 *                       a1, a2 = optional arguments or data fields
 *
 */

typedef enum
{
	MESSAGE_EMPTY = 0,

	/*	ARDUCON MESSAGE FAMILY (SERIAL MESSAGING) */
	MESSAGE_SET_FOX = 'F' * 100 + 'O' * 10 + 'X',           /* Set the fox role to be used to define timing and signals */
#if !SUPPORT_ONLY_80M
	MESSAGE_SET_AM_TONE = 'A' * 10 + 'M',					/* Set AM audio tone frequency */
#endif // !SUPPORT_ONLY_80M
	MESSAGE_UTIL = 'U' * 100 + 'T' * 10 + 'I',              /* Temperature  and Voltage data */
	MESSAGE_SET_STATION_ID = 'I' * 10 + 'D',                /* Sets amateur radio callsign text */
	MESSAGE_SYNC = 'S' * 100 + 'Y' * 10 + 'N',              /* Synchronizes transmissions */
	MESSAGE_CODE_SETTINGS = 'S' * 100 + 'E' * 10 + 'T',     /* Set Morse code speeds */
	MESSAGE_CLOCK = 'C' * 100 + 'L' * 10 + 'K',             /* Set or read the RTC */
	MESSAGE_PASSWORD = 'P' * 100 + 'W' * 10 + 'D',			/* Password command */
	MESSAGE_INFO = 'I' * 100 + 'N' * 10 + 'F',              /* Report firmware/update identity */
	MESSAGE_UPDATE = 'U' * 100 + 'P' * 10 + 'D',            /* Reboot into bootloader update mode */

	INVALID_MESSAGE = UINT16_MAX                            /* This value must never overlap a valid message ID */
} LBMessageID;

typedef enum
{
	LINKBUS_MSG_UNKNOWN = 0,
	LINKBUS_MSG_COMMAND,
	LINKBUS_MSG_QUERY,
	LINKBUS_MSG_REPLY,
	LINKBUS_MSG_INVALID
} LBMessageType;

typedef enum
{
	FIELD1 = 0,
	FIELD2 = 1
} LBMessageField;

typedef enum
{
	BATTERY_BROADCAST = 0x0001,
	RSSI_BROADCAST = 0x0002,
	RF_BROADCAST = 0x0004,
	UPC_TEMP_BROADCAST = 0x0008,
	ALL_BROADCASTS = 0x000FF
} LBbroadcastType;

typedef enum
{
	NO_ID = 0,
	CONTROL_HEAD_ID = 1,
	RECEIVER_ID = 2,
	TRANSMITTER_ID = 3
} DeviceID;

typedef char LinkbusTxBuffer[LINKBUS_MAX_TX_MSG_LENGTH];

typedef struct
{
	LBMessageType type;
	LBMessageID id;
	char fields[LINKBUS_MAX_MSG_NUMBER_OF_FIELDS][LINKBUS_MAX_MSG_FIELD_LENGTH];
} LinkbusRxBuffer;

#define WAITING_FOR_UPDATE -1

/**
 */
void linkbus_init(uint32_t baud);

/**
 * Immediately turns off receiver and flushes receive buffer
 */
void linkbus_disable(void);

/**
 * Undoes linkbus_disable()
 */
// void linkbus_enable(void);


/**
 */
void linkbus_end_tx(void);

/**
 */
// void linkbus_reset_rx(void);

/**
 */
LinkbusTxBuffer* nextEmptyTxBuffer(void);

/**
 */
LinkbusTxBuffer* nextFullTxBuffer(void);

/**
 */
BOOL linkbusTxInProgress(void);

/**
 */
LinkbusRxBuffer* nextEmptyRxBuffer(void);

/**
 */
LinkbusRxBuffer* nextFullRxBuffer(void);

/**
 */
void lb_send_NewPrompt(void);

/**
 */
void lb_send_NewLine(void);

/**
 */
void lb_echo_char(uint8_t c);

/**
 */
BOOL lb_send_string(char* str, BOOL wait);

/**
 */
void lb_send_value(uint16_t value, char* label);

/**
 */
BOOL lb_enabled(void);

#ifdef __cplusplus
	}
#endif

#endif  /* LINKBUS_H_ */
